gab-k/FlexAudioLink/firmware/src/prop/session.c

#include "prop/session.h"

#include <string.h>

#include <zephyr/logging/log.h>
#include <zephyr/sys/__assert.h>
#include <zephyr/sys/util.h>

LOG_MODULE_REGISTER(prop_session, CONFIG_LOG_DEFAULT_LEVEL);

#define PROP_SESSION_THREAD_STACK_SIZE       2048
#define PROP_SESSION_THREAD_PRIORITY         6
#define PROP_SESSION_QUEUE_DEPTH             4
#define PROP_SESSION_SYNC_LOSS_TURNS         8U

struct session_stats {
	uint32_t packets_lost_in_service;
	uint32_t loss_burst_1_count;
	uint32_t loss_burst_2_count;
	uint32_t loss_burst_3_4_count;
	uint32_t loss_burst_5_plus_count;
	uint32_t max_loss_burst_len;
	uint32_t outage_count;
	uint32_t rx_incomplete_count;
	uint32_t tx_trigger_fail_count;
};

struct prop_session_runtime {
	enum prop_session_state service_state;
	struct session_stats stats;
	uint8_t consecutive_rx_misses;
	uint64_t in_service_since_cyc;
	uint16_t next_tx_seq;
	uint16_t last_rx_seq;
	bool have_last_rx_seq;
	struct k_mutex mutex_lock;
};

static struct prop_session_runtime session = {
	.service_state = PROP_SESSION_STATE_NO_SERVICE,
	.mutex_lock = Z_MUTEX_INITIALIZER(session.mutex_lock),
};

static bool prop_session_copy_to_radio_rb(void);

K_MSGQ_DEFINE(prop_tx_queue, sizeof(struct prop_packet), PROP_SESSION_QUEUE_DEPTH, 4);
K_MSGQ_DEFINE(prop_rx_queue, sizeof(struct prop_packet), PROP_SESSION_QUEUE_DEPTH, 4);

static K_THREAD_STACK_DEFINE(prop_session_thread_stack, PROP_SESSION_THREAD_STACK_SIZE);
static struct k_thread prop_session_thread_data;

static void prop_session_thread(void *arg1, void *arg2, void *arg3);

static bool prop_session_seq_gap_from_expected(uint16_t expected, uint16_t seq, uint16_t *gap)
{
	uint16_t delta = (uint16_t)(seq - expected);

	if (delta == 0U) {
		*gap = 0U;
		return true;
	}

	if (delta < 0x8000U) {
		*gap = delta;
		return true;
	}

	return false;
}

static uint16_t prop_session_next_payload_seq(uint16_t seq)
{
	seq++;
	if (seq == PROP_KEEPALIVE_SEQ) {
		seq++;
	}

	return seq;
}

static void prop_session_reset_runtime(enum prop_session_state service_state)
{
	session.service_state = service_state;
	memset(&session.stats, 0, sizeof(session.stats));
	session.consecutive_rx_misses = 0U;
	session.in_service_since_cyc = 0U;
	session.next_tx_seq = 0U;
	session.last_rx_seq = 0U;
	session.have_last_rx_seq = false;
}

static bool prop_session_abort_enable(void)
{
	prop_radio_stop();

	session.service_state = PROP_SESSION_STATE_NO_SERVICE;

	return false;
}

static bool prop_session_start_radio(void)
{
	prop_radio_start();
	while (prop_session_copy_to_radio_rb()) {
	}

	return true;
}

static void prop_session_record_loss_burst(uint32_t burst_len)
{
	if (burst_len == 0U) {
		return;
	}

	if (burst_len == 1U) {
		session.stats.loss_burst_1_count++;
	} else if (burst_len == 2U) {
		session.stats.loss_burst_2_count++;
	} else if (burst_len <= 4U) {
		session.stats.loss_burst_3_4_count++;
	} else {
		session.stats.loss_burst_5_plus_count++;
	}

	if (burst_len > session.stats.max_loss_burst_len) {
		session.stats.max_loss_burst_len = burst_len;
	}
}

static void prop_session_enter_in_service(void)
{
	if (session.service_state == PROP_SESSION_STATE_IN_SERVICE) {
		return;
	}

	session.service_state = PROP_SESSION_STATE_IN_SERVICE;
	session.consecutive_rx_misses = 0U;
	session.in_service_since_cyc = k_cycle_get_64();
	LOG_INF("service established");
}

static void prop_session_mark_no_service(void)
{
	bool was_in_service = (session.service_state == PROP_SESSION_STATE_IN_SERVICE);

	if (was_in_service) {
		session.stats.outage_count++;
	}

	session.service_state = PROP_SESSION_STATE_NO_SERVICE;
	session.consecutive_rx_misses = 0U;
	session.in_service_since_cyc = 0U;
	session.have_last_rx_seq = false;

	if (was_in_service) {
		LOG_WRN("service outage (listen timeouts)");
	}
}

static void prop_session_record_in_service_rx(uint16_t seq)
{
	if (session.have_last_rx_seq) {
		uint16_t expected = prop_session_next_payload_seq(session.last_rx_seq);
		uint16_t gap;

		if (prop_session_seq_gap_from_expected(expected, seq, &gap) && gap > 0U) {
			session.stats.packets_lost_in_service += gap;
			prop_session_record_loss_burst(gap);
		}
	}

	session.last_rx_seq = seq;
	session.have_last_rx_seq = true;
}

static bool prop_session_packet_len_is_valid(uint8_t packet_len)
{
	return packet_len > PROP_PACKET_METADATA_LEN &&
	       packet_len <= PROP_PACKET_MAX_LEN;
}

static bool prop_session_is_keepalive_packet(const struct prop_packet *packet)
{
	if (packet == NULL) {
		__ASSERT_NO_MSG(0);
		return false;
	}

	return packet->length == PROP_KEEPALIVE_LEN && packet->seq == PROP_KEEPALIVE_SEQ;
}

static bool prop_session_copy_to_radio_rb(void)
{
	struct prop_packet *radio_packet;
	struct prop_packet queued_packet;
	uint8_t payload_bytes;

	radio_packet = prop_radio_tx_get_wr_ptr();
	if (radio_packet == NULL) {
		return false;
	}

	if (k_msgq_get(&prop_tx_queue, &queued_packet, K_NO_WAIT) != 0) {
		return false;
	}

	if (!prop_session_packet_len_is_valid(queued_packet.length)) {
		LOG_ERR("copy_to_radio_rb packet length is invalid!");
		return false;
	}

	payload_bytes = queued_packet.length - PROP_PACKET_METADATA_LEN;
	memset(radio_packet, 0, sizeof(*radio_packet));
	radio_packet->length = queued_packet.length;
	radio_packet->seq = session.next_tx_seq;
	memcpy(radio_packet->data, queued_packet.data, payload_bytes);

	prop_radio_tx_advance_wr_idx();
	session.next_tx_seq = prop_session_next_payload_seq(session.next_tx_seq);
	return true;
}

static void prop_session_handle_rx_ok(const struct prop_session_event *event)
{
	const struct prop_packet *packet;
	bool is_keepalive;

	if (event == NULL) {
		__ASSERT_NO_MSG(0);
		return;
	}

	packet = prop_radio_rx_get_rd_ptr();
	if (packet == NULL) {
		__ASSERT_NO_MSG(0);
		return;
	}

	is_keepalive = prop_session_is_keepalive_packet(packet);
	if (!prop_session_packet_len_is_valid(packet->length)) {
		LOG_ERR("rx_handle_ok packet length is invalid!");
		prop_radio_rx_advance_rd_idx();
		return;
	}

	session.consecutive_rx_misses = 0U;
	prop_session_enter_in_service();

	if (!is_keepalive) {
		(void)k_msgq_put(&prop_rx_queue, packet, K_NO_WAIT);
		prop_session_record_in_service_rx(packet->seq);
	}

	prop_radio_rx_advance_rd_idx();
}

static void prop_session_handle_rx_bad(const struct prop_session_event *event)
{
	if (event == NULL) {
		__ASSERT_NO_MSG(0);
		return;
	}

	session.consecutive_rx_misses = 0U;
	prop_radio_rx_advance_rd_idx();
}

static void prop_session_handle_tx_end(const struct prop_session_event *event)
{
	if (event == NULL) {
		__ASSERT_NO_MSG(0);
		return;
	}

	while (prop_session_copy_to_radio_rb()) {
	}
}

static void prop_session_handle_listen_timeout(void)
{
	if (session.service_state == PROP_SESSION_STATE_IN_SERVICE) {
		session.consecutive_rx_misses++;
		if (session.consecutive_rx_misses >= PROP_SESSION_SYNC_LOSS_TURNS) {
			prop_session_mark_no_service();
			return;
		}
	} else {
		LOG_WRN_RATELIMIT_RATE(10000, "Waiting for PROP peer...");
	}
}

static bool prop_session_start_with_role(void (*set_role)(void))
{
	bool started;

	prop_radio_init();

	k_mutex_lock(&session.mutex_lock, K_FOREVER);
	prop_session_reset_runtime(PROP_SESSION_STATE_NO_SERVICE);
	set_role();
	started = prop_session_start_radio();
	k_mutex_unlock(&session.mutex_lock);

	k_thread_create(&prop_session_thread_data, prop_session_thread_stack,
			K_THREAD_STACK_SIZEOF(prop_session_thread_stack),
			prop_session_thread, NULL, NULL, NULL,
			PROP_SESSION_THREAD_PRIORITY, 0, K_NO_WAIT);

	return started;
}

bool prop_session_start_dongle(void)
{
	return prop_session_start_with_role(prop_radio_set_role_dongle);
}

bool prop_session_start_headset(void)
{
	return prop_session_start_with_role(prop_radio_set_role_headset);
}

enum prop_session_state prop_session_get_state(void)
{
	enum prop_session_state state;

	k_mutex_lock(&session.mutex_lock, K_FOREVER);
	state = session.service_state;
	k_mutex_unlock(&session.mutex_lock);
	return state;
}

void prop_session_get_report(struct prop_session_report *report)
{
	struct prop_radio_stats radio_stats;
	struct session_stats stats;
	enum prop_session_state state;
	uint64_t in_service_since_cyc;
	uint64_t time_in_service_us = 0U;

	if (report == NULL) {
		return;
	}

	prop_radio_get_stats(&radio_stats);

	k_mutex_lock(&session.mutex_lock, K_FOREVER);
	stats = session.stats;
	state = session.service_state;
	in_service_since_cyc = session.in_service_since_cyc;
	k_mutex_unlock(&session.mutex_lock);

	if (state == PROP_SESSION_STATE_IN_SERVICE && in_service_since_cyc != 0U) {
		time_in_service_us = k_cyc_to_us_floor64(k_cycle_get_64() - in_service_since_cyc);
	}

	*report = (struct prop_session_report){
		.packets_tx = radio_stats.packets_tx,
		.rx_ok_count = radio_stats.rx_ok_count,
		.packets_lost_in_service = stats.packets_lost_in_service,
		.loss_burst_1_count = stats.loss_burst_1_count,
		.loss_burst_2_count = stats.loss_burst_2_count,
		.loss_burst_3_4_count = stats.loss_burst_3_4_count,
		.loss_burst_5_plus_count = stats.loss_burst_5_plus_count,
		.max_loss_burst_len = stats.max_loss_burst_len,
		.crc_error_count = radio_stats.crc_errors,
		.deadline_late_count = radio_stats.deadline_late_count,
		.rx_incomplete_count = stats.rx_incomplete_count,
		.tx_trigger_fail_count = stats.tx_trigger_fail_count,
		.outage_count = stats.outage_count,
		.time_in_service_us = time_in_service_us,
		.last_rssi_dbm = radio_stats.last_rssi_dbm,
		.state = state,
	};
}

bool prop_session_tx_enqueue(const struct prop_packet *packet, k_timeout_t timeout)
{
	if (packet == NULL) {
		LOG_ERR("tx_enqueue packet pointer is NULL!");
		return false;
	}

	if (!prop_session_packet_len_is_valid(packet->length)) {
		LOG_ERR("tx_enqueue packet length is invalid!");
		return false;
	}

	return k_msgq_put(&prop_tx_queue, packet, timeout) == 0;
}

bool prop_session_rx_dequeue(struct prop_packet *packet, k_timeout_t timeout)
{
	if (packet == NULL) {
		LOG_ERR("rx_dequeue packet pointer is NULL!");
		return false;
	}

	return k_msgq_get(&prop_rx_queue, packet, timeout) == 0;
}

static void prop_session_thread(void *arg1, void *arg2, void *arg3)
{
	struct prop_session_event event;

	ARG_UNUSED(arg1);
	ARG_UNUSED(arg2);
	ARG_UNUSED(arg3);

	while (1) {
		if (!prop_radio_dequeue_session_event(&event, K_FOREVER)) {
			continue;
		}

		k_mutex_lock(&session.mutex_lock, K_FOREVER);
		switch (event.type) {
		case PROP_RADIO_SESSION_EVENT_RX_OK:
			prop_session_handle_rx_ok(&event);
			break;
		case PROP_RADIO_SESSION_EVENT_RX_BAD:
			prop_session_handle_rx_bad(&event);
			break;
		case PROP_RADIO_SESSION_EVENT_TX_END:
			prop_session_handle_tx_end(&event);
			break;
		case PROP_RADIO_SESSION_EVENT_RX_INCOMPLETE:
			session.stats.rx_incomplete_count++;
			session.consecutive_rx_misses = 0U;
			break;
		case PROP_RADIO_SESSION_EVENT_LISTEN_TIMEOUT:
			prop_session_handle_listen_timeout();
			break;
		case PROP_RADIO_SESSION_EVENT_TX_TRIGGER_FAILED:
			session.stats.tx_trigger_fail_count++;
			prop_session_mark_no_service();
			LOG_ERR("failed to trigger prepared TX");
			(void)prop_session_abort_enable();
			break;
		default:
			break;
		}
		k_mutex_unlock(&session.mutex_lock);
	}
}
