gab-k/FlexAudioLink/firmware/src/audio/path_dongle.c

#include "audio/path_dongle.h"

#include <string.h>
#include <zephyr/kernel.h>
#include <zephyr/logging/log.h>
LOG_MODULE_REGISTER(path_dongle, LOG_LEVEL_INF);
#include "tusb.h"
#include "prop/session.h"

#define PATH_DONGLE_LATENCY_MARKER_GPIO

#define DONGLE_THREAD_STACK_SIZE  3072
#define DONGLE_THREAD_PRIORITY    6
#define DONGLE_LOOP_SLEEP_MS      1

#ifdef PATH_DONGLE_LATENCY_MARKER_GPIO
#include <hal/nrf_gpio.h>
#define DONGLE_LATENCY_MARKER_PIN NRF_GPIO_PIN_MAP(0U, 2U)

static const uint8_t latency_marker_pattern[] = {
	0xff, 0x7f, 0xff, 0x7f, /* L/R +32767 */
	0x00, 0x80, 0x00, 0x80, /* L/R -32768 */
	0xff, 0x7f, 0xff, 0x7f, /* L/R +32767 */
	0x00, 0x80, 0x00, 0x80, /* L/R -32768 */
};

static void latency_marker_gpio_init(void)
{
	nrf_gpio_cfg_output(DONGLE_LATENCY_MARKER_PIN);
	nrf_gpio_pin_clear(DONGLE_LATENCY_MARKER_PIN);
}

static void latency_marker_gpio_toggle(void)
{
	nrf_gpio_pin_toggle(DONGLE_LATENCY_MARKER_PIN);
}

static bool latency_marker_payload_has_pattern(const uint8_t *payload, uint32_t payload_bytes)
{
	if (payload == NULL || payload_bytes < sizeof(latency_marker_pattern)) {
		return false;
	}

	for (uint32_t i = 0U; i <= payload_bytes - sizeof(latency_marker_pattern); i += 2U) {
		if (memcmp(&payload[i], latency_marker_pattern,
			   sizeof(latency_marker_pattern)) == 0) {
			return true;
		}
	}

	return false;
}
#else
static inline void latency_marker_gpio_init(void) {
}

static inline void latency_marker_gpio_toggle(void) {
}

static inline bool latency_marker_payload_has_pattern(const uint8_t *payload, uint32_t payload_bytes)
{
	ARG_UNUSED(payload);
	ARG_UNUSED(payload_bytes);
	return false;
}
#endif

static struct path_dongle_status dongle_status;

K_SEM_DEFINE(dongle_usb_audio_rx_sem, 0, 1);

static K_THREAD_STACK_DEFINE(dongle_thread_stack, DONGLE_THREAD_STACK_SIZE);
static struct k_thread dongle_thread_data;

static void dongle_thread(void *a, void *b, void *c);

void path_dongle_init(void)
{
	k_thread_create(&dongle_thread_data, dongle_thread_stack,
			K_THREAD_STACK_SIZEOF(dongle_thread_stack),
			dongle_thread, NULL, NULL, NULL,
			DONGLE_THREAD_PRIORITY, 0, K_NO_WAIT);
}

void path_dongle_get_status(struct path_dongle_status *out)
{
	if (out != NULL) {
		*out = dongle_status;
	}
}

void path_dongle_wake_thread(void)
{
	k_sem_give(&dongle_usb_audio_rx_sem);
}

static void dongle_thread(void *a, void *b, void *c)
{
	ARG_UNUSED(a);
	ARG_UNUSED(b);
	ARG_UNUSED(c);

	tu_fifo_t *ep_out_ff = NULL;
	tu_fifo_t *ep_in_ff = NULL;

	latency_marker_gpio_init();

	while (ep_out_ff == NULL || ep_in_ff == NULL) {
		ep_out_ff = tud_audio_get_ep_out_ff();
		ep_in_ff = tud_audio_get_ep_in_ff();
		k_sleep(K_MSEC(DONGLE_LOOP_SLEEP_MS));
	}

	while (1) {
		/* PROP RX → USB mic EP IN */
		while (1) {
			struct prop_packet packet;
			uint8_t payload_bytes;

			uint16_t ep_in_remaining = tu_fifo_remaining(ep_in_ff);
			if(ep_in_remaining < PROP_MIC_PACKET_BYTES) {
				break;
			}

			if (!prop_session_rx_dequeue(&packet, K_NO_WAIT)) {
				break;
			}

			payload_bytes = packet.length - PROP_PACKET_METADATA_LEN;
			if (payload_bytes != PROP_MIC_PACKET_BYTES) {
				LOG_ERR("Invalid payload size! Expected %d bytes, got %d bytes", PROP_MIC_PACKET_BYTES, payload_bytes);
				break;
			}

			uint16_t written = tu_fifo_write_n(ep_in_ff, packet.data, payload_bytes);
			if (written != payload_bytes) {
				LOG_ERR("Invalid bytes written to USB EP IN FIFO! Expected %d bytes, wrote %d bytes", payload_bytes, written);
				break;
			}
		}

		/* USB EP OUT FIFO → PROP TX */
		while(1) {
			struct prop_packet packet;
			uint32_t payload_bytes;

			uint16_t ep_out_count = tu_fifo_count(ep_out_ff);
			if(ep_out_count < PROP_SPK_PACKET_BYTES) {
				break;
			}
			
			memset(&packet, 0, sizeof(packet));
			payload_bytes = tu_fifo_read_n(ep_out_ff, packet.data, PROP_SPK_PACKET_BYTES);

			if (payload_bytes != PROP_SPK_PACKET_BYTES) {
				LOG_ERR("Invalid payload size from USB EP OUT! Expected %d bytes, got %d bytes", PROP_SPK_PACKET_BYTES, payload_bytes);
				break;
			}

			if (latency_marker_payload_has_pattern(packet.data, payload_bytes)) {
				latency_marker_gpio_toggle();
			}

			packet.length = PROP_PACKET_METADATA_LEN + PROP_SPK_PACKET_BYTES;

			if (!prop_session_tx_enqueue(&packet, K_NO_WAIT)) {
				dongle_status.overflow_bytes += payload_bytes;
				break;
			}
		}

		k_sem_take(&dongle_usb_audio_rx_sem, K_MSEC(DONGLE_LOOP_SLEEP_MS));
	}
}
