gab-k/FlexAudioLink/Dongle_ESPNOW/main/espnow_example_main.c

// File: espnow_tx.c
#include "freertos/FreeRTOS.h"
#include "freertos/task.h"
#include "esp_log.h"
#include "esp_now.h"
#include "esp_wifi.h"
#include "esp_mac.h"
#include "nvs_flash.h"
#include "driver/gpio.h"

static const char *TAG = "ESPNOW_TX";

// ================== CONFIGURATION ==================
// Set the GPIO pin to toggle on send
#define GPIO_OUTPUT_PIN     GPIO_NUM_15

// Replace this with the MAC address of your Headset (RX) device
static uint8_t peer_mac_address[] = {0x40, 0x4C, 0xCA, 0x4F, 0x3E, 0x18};
// ===================================================

// Define a simple data structure for the packet
typedef struct {
    uint32_t count;
    uint8_t  payload[1344]; // 7ms audio 48kHz Stereo 16 Bit
} audio_packet_t;

// Callback function for when a packet is sent
void on_data_sent(const esp_now_send_info_t *tx_info, esp_now_send_status_t status) {
    // Set the GPIO low AFTER the transmission is confirmed
    if (status != ESP_NOW_SEND_SUCCESS) {
        ESP_LOGE(TAG, "Send failed");
    }
}

static const uint8_t sine_wave_pcm[] = {
    0x00, 0x00, 0x00, 0x00, 0x64, 0x02, 0xcb, 0x17, 0xc9, 0x04, 0xc3, 0x2e,
    0x2d, 0x07, 0x19, 0x44, 0x90, 0x09, 0x0f, 0x57, 0xf3, 0x0b, 0xfc, 0x66,
    0x54, 0x0e, 0x52, 0x73, 0xb4, 0x10, 0xa2, 0x7b, 0x13, 0x13, 0xa3, 0x7f,
    0x70, 0x15, 0x30, 0x7f, 0xcb, 0x17, 0x4f, 0x7a, 0x24, 0x1a, 0x29, 0x71,
    0x7b, 0x1c, 0x12, 0x64, 0xcf, 0x1e, 0x7d, 0x53, 0x20, 0x21, 0xff, 0x3f,
    0x6f, 0x23, 0x46, 0x2a, 0xba, 0x25, 0x13, 0x13, 0x02, 0x28, 0x37, 0xfb,
    0x46, 0x2a, 0x85, 0xe3, 0x86, 0x2c, 0xd1, 0xcc, 0xc3, 0x2e, 0xe6, 0xb7,
    0xfb, 0x30, 0x7f, 0xa5, 0x2f, 0x33, 0x3f, 0x96, 0x5e, 0x35, 0xb0, 0x8a,
    0x89, 0x37, 0x37, 0x83, 0xae, 0x39, 0x18, 0x80, 0xce, 0x3b, 0x6f, 0x81,
    0xea, 0x3d, 0x30, 0x87, 0xff, 0x3f, 0x27, 0x91, 0x0f, 0x42, 0xfc, 0x9e,
    0x19, 0x44, 0x33, 0xb0, 0x1c, 0x46, 0x31, 0xc4, 0x1a, 0x48, 0x46, 0xda,
    0x11, 0x4a, 0xac, 0xf1, 0x01, 0x4c, 0x90, 0x09, 0xeb, 0x4d, 0x20, 0x21,
    0xcd, 0x4f, 0x89, 0x37, 0xa9, 0x51, 0x01, 0x4c, 0x7d, 0x53, 0xd3, 0x5d,
    0x4a, 0x55, 0x60, 0x6c, 0x0f, 0x57, 0x25, 0x77, 0xcc, 0x58, 0xc3, 0x7d,
    0x81, 0x5a, 0xfe, 0x7f, 0x2e, 0x5c, 0xc3, 0x7d, 0xd3, 0x5d, 0x25, 0x77,
    0x70, 0x5f, 0x60, 0x6c, 0x04, 0x61, 0xd3, 0x5d, 0x8f, 0x62, 0x01, 0x4c,
    0x12, 0x64, 0x89, 0x37, 0x8b, 0x65, 0x20, 0x21, 0xfc, 0x66, 0x90, 0x09,
    0x63, 0x68, 0xac, 0xf1, 0xc1, 0x69, 0x46, 0xda, 0x15, 0x6b, 0x32, 0xc4,
    0x60, 0x6c, 0x33, 0xb0, 0xa1, 0x6d, 0xfc, 0x9e, 0xd9, 0x6e, 0x27, 0x91,
    0x06, 0x70, 0x30, 0x87, 0x29, 0x71, 0x6f, 0x81, 0x43, 0x72, 0x18, 0x80,
    0x52, 0x73, 0x37, 0x83, 0x56, 0x74, 0xaf, 0x8a, 0x50, 0x75, 0x3f, 0x96,
    0x40, 0x76, 0x7f, 0xa5, 0x25, 0x77, 0xe6, 0xb7, 0x00, 0x78, 0xd1, 0xcc,
    0xd0, 0x78, 0x85, 0xe3, 0x95, 0x79, 0x37, 0xfb, 0x4f, 0x7a, 0x13, 0x13,
    0xfe, 0x7a, 0x46, 0x2a, 0xa2, 0x7b, 0xff, 0x3f, 0x3b, 0x7c, 0x7d, 0x53,
    0xc9, 0x7c, 0x12, 0x64, 0x4c, 0x7d, 0x29, 0x71, 0xc3, 0x7d, 0x4f, 0x7a,
    0x30, 0x7e, 0x30, 0x7f, 0x91, 0x7e, 0xa3, 0x7f, 0xe6, 0x7e, 0xa2, 0x7b,
    0x30, 0x7f, 0x52, 0x73, 0x6f, 0x7f, 0xfc, 0x66, 0xa3, 0x7f, 0x0f, 0x57,
    0xcb, 0x7f, 0x19, 0x44, 0xe8, 0x7f, 0xc3, 0x2e, 0xf9, 0x7f, 0xcb, 0x17,
    0xfe, 0x7f, 0x00, 0x00, 0xf9, 0x7f, 0x35, 0xe8, 0xe8, 0x7f, 0x3e, 0xd1,
    0xcb, 0x7f, 0xe8, 0xbb, 0xa3, 0x7f, 0xf1, 0xa8, 0x6f, 0x7f, 0x04, 0x99,
    0x30, 0x7f, 0xaf, 0x8c, 0xe6, 0x7e, 0x5e, 0x84, 0x91, 0x7e, 0x5d, 0x80,
    0x30, 0x7e, 0xd0, 0x80, 0xc3, 0x7d, 0xb1, 0x85, 0x4c, 0x7d, 0xd7, 0x8e,
    0xc9, 0x7c, 0xee, 0x9b, 0x3b, 0x7c, 0x83, 0xac, 0xa2, 0x7b, 0x01, 0xc0,
    0xfe, 0x7a, 0xba, 0xd5, 0x4f, 0x7a, 0xed, 0xec, 0x95, 0x79, 0xc9, 0x04,
    0xd0, 0x78, 0x7b, 0x1c, 0x00, 0x78, 0x2f, 0x33, 0x25, 0x77, 0x1a, 0x48,
    0x40, 0x76, 0x81, 0x5a, 0x51, 0x75, 0xc1, 0x69, 0x56, 0x74, 0x50, 0x75,
    0x52, 0x73, 0xc9, 0x7c, 0x43, 0x72, 0xe8, 0x7f, 0x29, 0x71, 0x91, 0x7e,
    0x06, 0x70, 0xd0, 0x78, 0xd9, 0x6e, 0xd9, 0x6e, 0xa1, 0x6d, 0x04, 0x61,
    0x60, 0x6c, 0xce, 0x4f, 0x15, 0x6b, 0xcf, 0x3b, 0xc1, 0x69, 0xba, 0x25,
    0x63, 0x68, 0x54, 0x0e, 0xfc, 0x66, 0x70, 0xf6, 0x8b, 0x65, 0xe0, 0xde,
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
};

void app_main(void) {
    // Initialize NVS
    esp_err_t ret = nvs_flash_init();
    if (ret == ESP_ERR_NVS_NO_FREE_PAGES || ret == ESP_ERR_NVS_NEW_VERSION_FOUND) {
        ESP_ERROR_CHECK(nvs_flash_erase());
        ret = nvs_flash_init();
    }
    ESP_ERROR_CHECK(ret);

    // Initialize networking stack
    ESP_ERROR_CHECK(esp_netif_init());
    ESP_ERROR_CHECK(esp_event_loop_create_default());
    wifi_init_config_t cfg = WIFI_INIT_CONFIG_DEFAULT();
    ESP_ERROR_CHECK(esp_wifi_init(&cfg));
    ESP_ERROR_CHECK(esp_wifi_set_storage(WIFI_STORAGE_RAM));
    ESP_ERROR_CHECK(esp_wifi_set_mode(WIFI_MODE_STA));
    ESP_ERROR_CHECK(esp_wifi_start());
    
    // Initialize GPIO
    gpio_reset_pin(GPIO_OUTPUT_PIN);
    gpio_set_direction(GPIO_OUTPUT_PIN, GPIO_MODE_OUTPUT);
    gpio_set_level(GPIO_OUTPUT_PIN, 0);
    
    // Initialize ESP-NOW
    ESP_ERROR_CHECK(esp_now_init());
    ESP_ERROR_CHECK(esp_now_register_send_cb(on_data_sent));
    
    // Add the peer (the Headset/Receiver)
    esp_now_peer_info_t peer_info = {};
    memcpy(peer_info.peer_addr, peer_mac_address, 6);
    peer_info.channel = 0; // 0 means use the current channel
    peer_info.ifidx = WIFI_IF_STA;
    peer_info.encrypt = false;
    ESP_ERROR_CHECK(esp_now_add_peer(&peer_info));
    
    esp_now_rate_config_t rate_config = {
                .phymode = WIFI_PHY_MODE_HE20,    
                .rate = WIFI_PHY_RATE_MCS9_SGI,     
                .ersu = false,                     
                .dcm = false                       
            };
    ESP_ERROR_CHECK(esp_now_set_peer_rate_config(peer_mac_address, &rate_config));

    ESP_LOGI(TAG, "Setup complete. Starting to send packets...");

    audio_packet_t packet_to_send;
    packet_to_send.count = 0;

    memcpy(packet_to_send.payload, sine_wave_pcm, sizeof(sine_wave_pcm));
    
    ESP_LOGI(TAG, "0x%x", packet_to_send.payload[4]);

    while (1) {
        // Set GPIO HIGH just before sending
        gpio_set_level(GPIO_OUTPUT_PIN, 1);
        gpio_set_level(GPIO_OUTPUT_PIN, 0);

        esp_err_t result = esp_now_send(peer_mac_address, (uint8_t *)&packet_to_send, sizeof(packet_to_send));
        
        if (result == ESP_OK) {
            if(packet_to_send.count%1000 == 0)
                ESP_LOGI(TAG, "Sent packet #%lu", packet_to_send.count);
        } else {
            ESP_LOGE(TAG, "Error sending packet: %s", esp_err_to_name(result));
        }

        packet_to_send.count++;
        vTaskDelay(pdMS_TO_TICKS(7));
    }
}
